JMUWRobotics/Raspberry-Pi-based-LiDAR-Camera-Rig/thesis/pics/c_pcl_extrinsic_calib.png

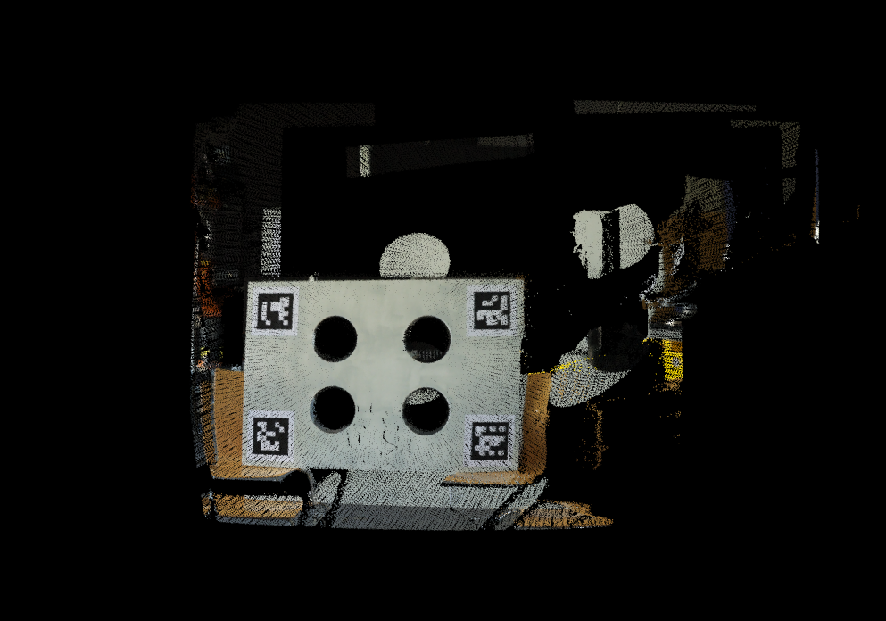
thesis/pics/c_pcl_extrinsic_calib.png
