JMUWRobotics/Raspberry-Pi-based-LiDAR-Camera-Rig/thesis/pics/captured_chessboards/chessboard_002_annotated.png

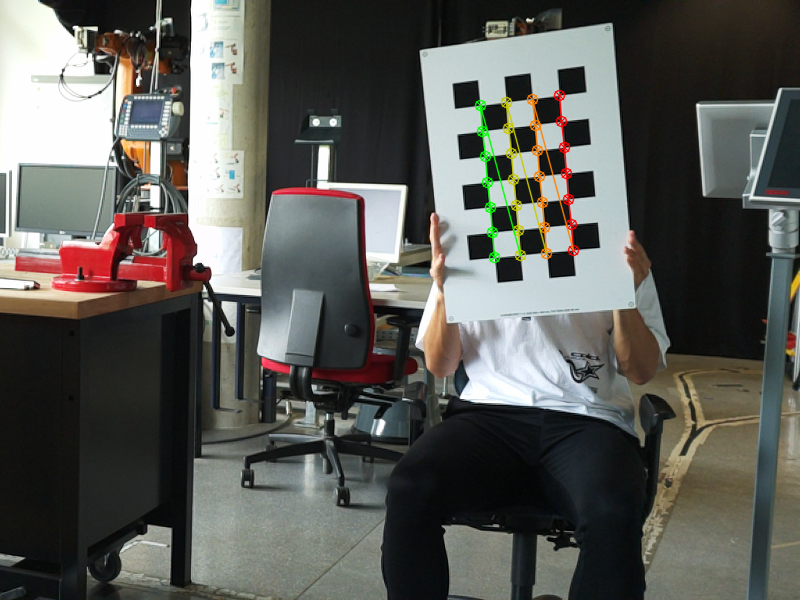
thesis/pics/captured_chessboards/chessboard_002_annotated.png
