JMUWRobotics/Raspberry-Pi-based-LiDAR-Camera-Rig/thesis/pics/chessboard_intrinsic.png

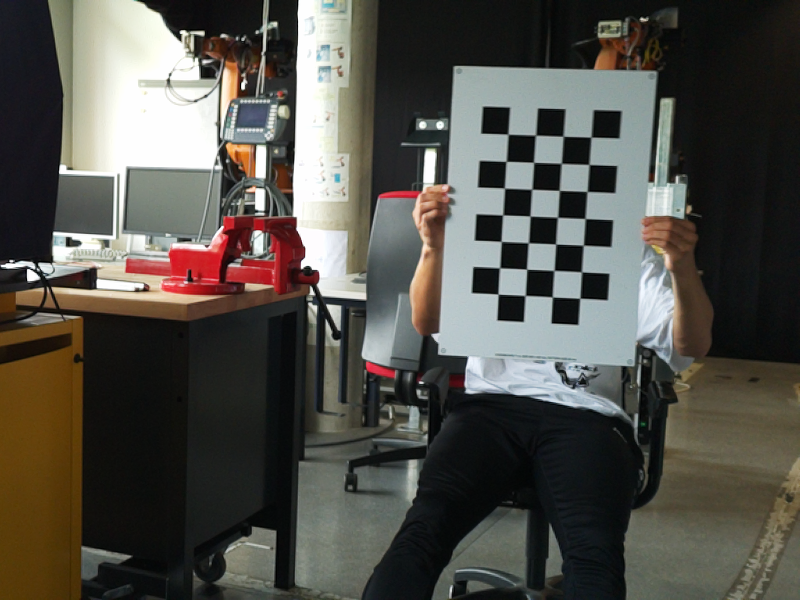
thesis/pics/chessboard_intrinsic.png
