JMUWRobotics/Raspberry-Pi-based-LiDAR-Camera-Rig/thesis/pics/depth_robohall.png

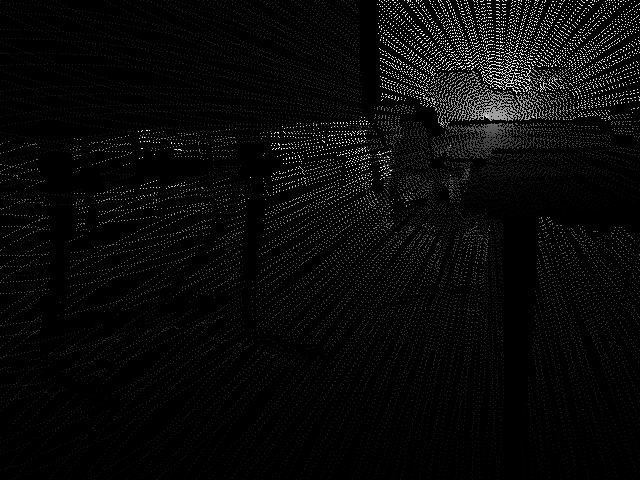
thesis/pics/depth_robohall.png
