JMUWRobotics/Raspberry-Pi-based-LiDAR-Camera-Rig/thesis/pics/Device Images/device_front.png

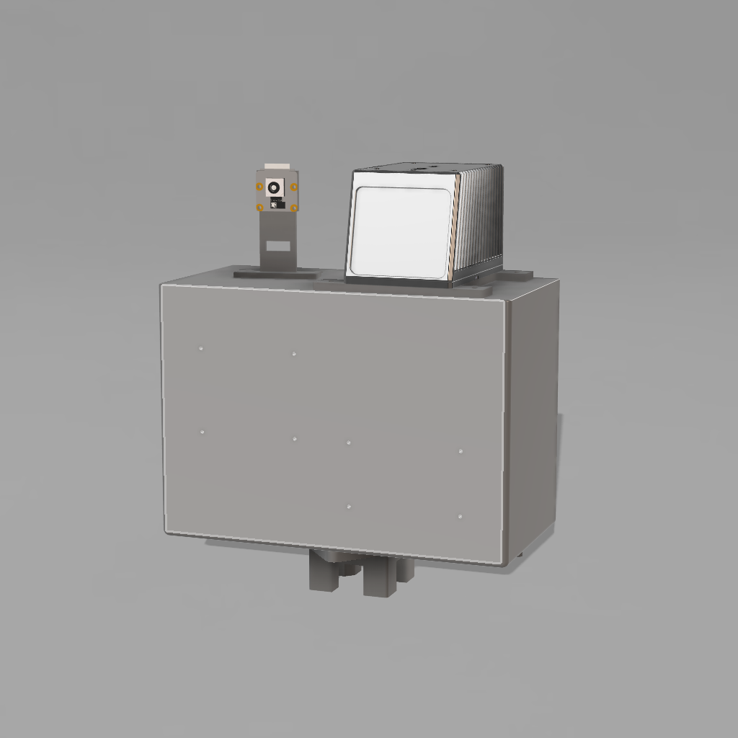
thesis/pics/Device Images/device_front.png
