JMUWRobotics/Raspberry-Pi-based-LiDAR-Camera-Rig/thesis/pics/Device Images/front_trnsparent.png

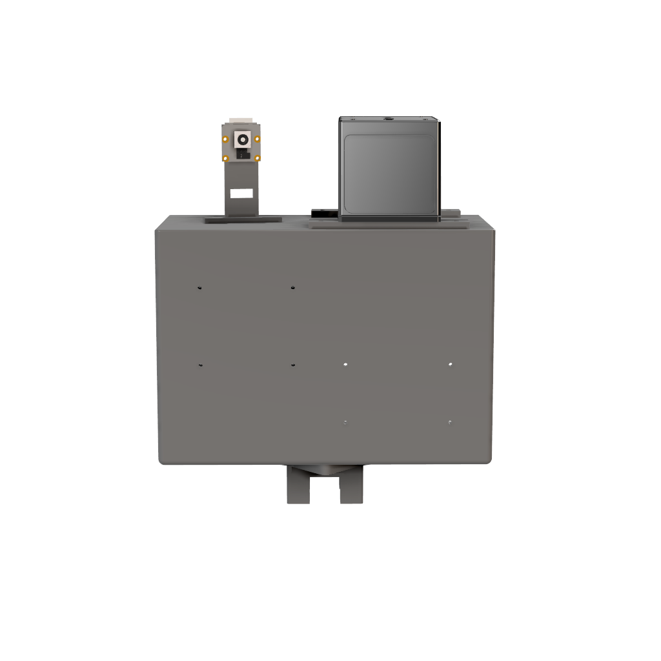
thesis/pics/Device Images/front_trnsparent.png
