JMUWRobotics/Raspberry-Pi-based-LiDAR-Camera-Rig/thesis/pics/Device Images/KUKA_Lab_depth_2.png

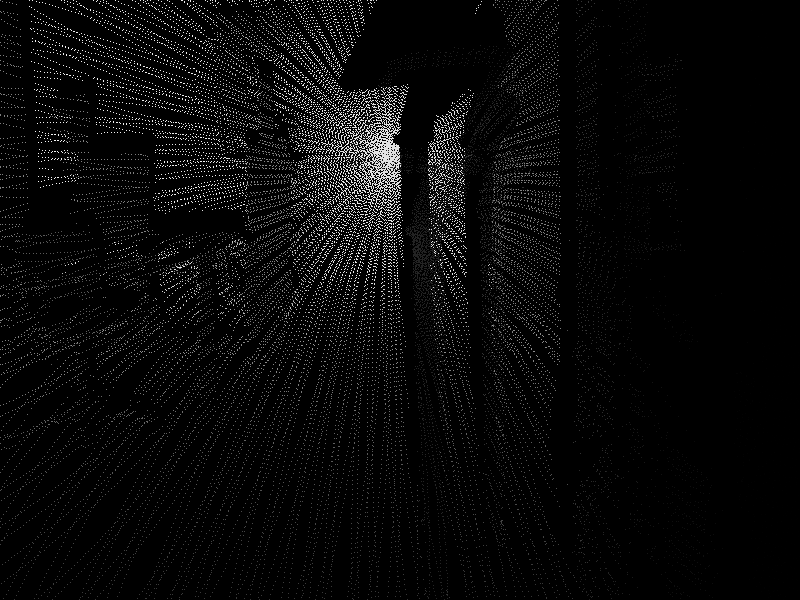
thesis/pics/Device Images/KUKA_Lab_depth_2.png
