JMUWRobotics/Raspberry-Pi-based-LiDAR-Camera-Rig/thesis/pics/extrinsic_calib_pattern.png

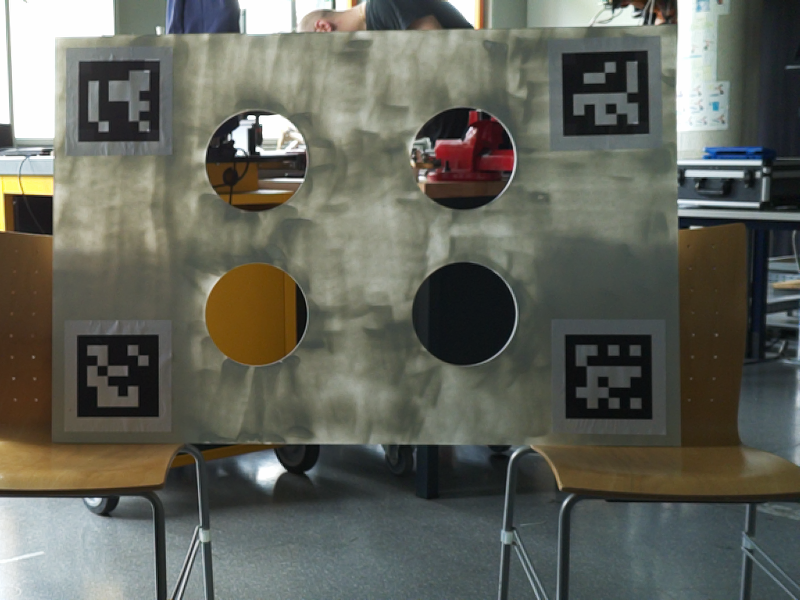
thesis/pics/extrinsic_calib_pattern.png
