JMUWRobotics/Raspberry-Pi-based-LiDAR-Camera-Rig/thesis/pics/qr_detect.png

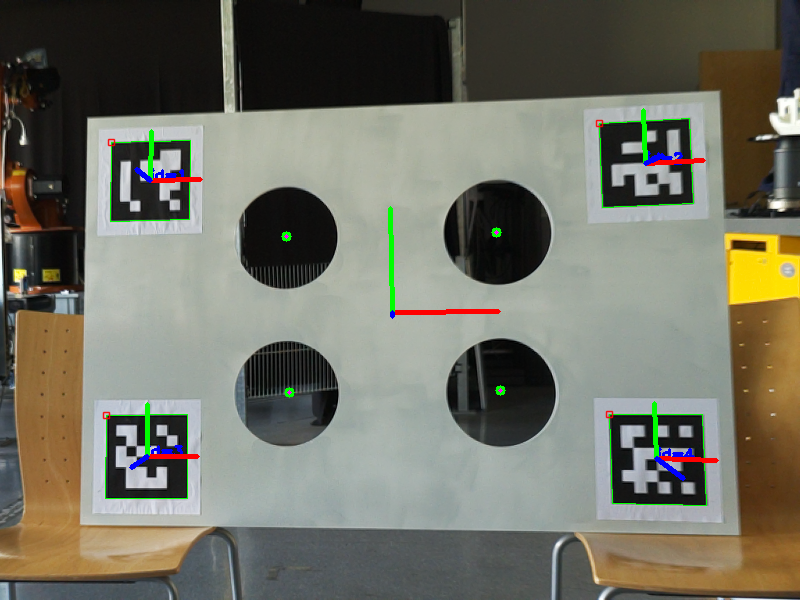
thesis/pics/qr_detect.png
