JMUWRobotics/Raspberry-Pi-based-LiDAR-Camera-Rig/thesis/pics/robo/robo_5/depth0016_aligned.png

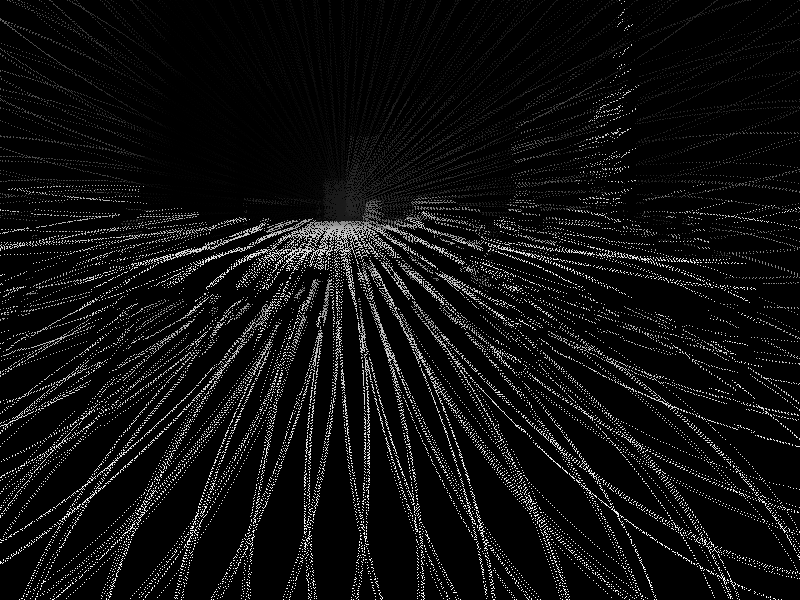
thesis/pics/robo/robo_5/depth0016_aligned.png
