JMUWRobotics/Raspberry-Pi-based-LiDAR-Camera-Rig/thesis/pics/robo/robo_5/Screenshot from 2025-09-14 18-28-05.png

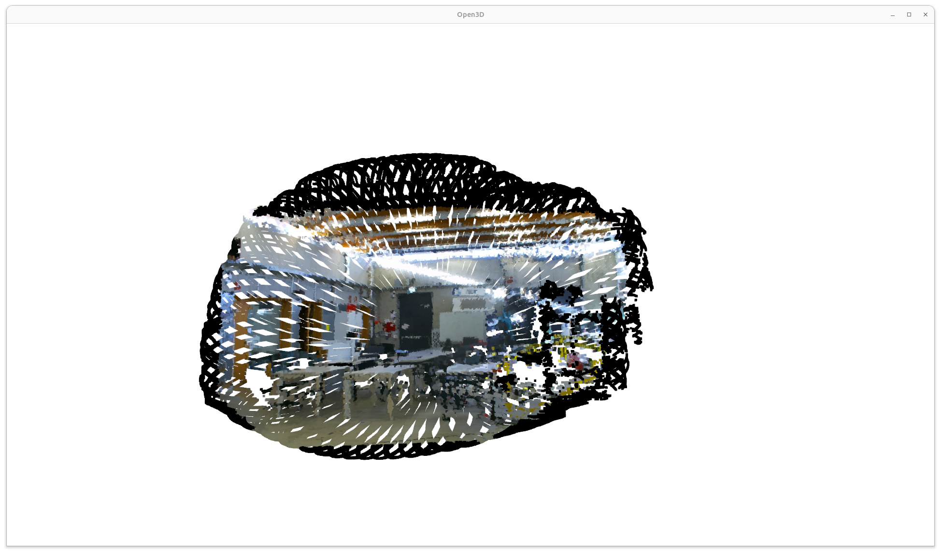
thesis/pics/robo/robo_5/Screenshot from 2025-09-14 18-28-05.png
